nichtrami/led_tube/test_programs/results/analysis/tables/range_hidden_metrics_full.csv

Messpunkt | duration_s | packets_recv | packets_expected | packets_lost | loss_pct | loss_win_mean_pct | loss_win_p95_pct | loss_win_max_pct | burst_max_steps | burst_max_ms | win_visible_pct | win_clean_pct | jitter_mean_ms | rssi_mean_dbm | rssi_min_dbm | recv_per_seq_mean | recv_per_seq_min
10 m | 299.0 | 11934 | 11992 | 58 | 0.48 | 0.4452 | 0.0 | 30.91 | 3 | 75 | 1.6666666666666667 | 97.66666666666667 | 6.9603 | -81.22833333333334 | -95.0 | 4.802133333333333 | 2.34
50 m | 299.0 | 11743 | 11993 | 250 | 2.08 | 2.066 | 10.081500000000018 | 41.46 | 9 | 225 | 7.333333333333333 | 64.33333333333333 | 9.229566666666667 | -77.85066666666665 | -95.0 | 3.574666666666666 | 1.33
100 m | 299.0 | 10691 | 11993 | 1302 | 10.86 | 10.8079 | 36.635500000000015 | 87.8 | 23 | 575 | 37.0 | 25.666666666666664 | 16.4451 | -82.965 | -95.0 | 2.7185 | 1.2
150 m | 299.0 | 8732 | 11992 | 3260 | 27.18 | 27.146799999999995 | 60.79900000000006 | 82.93 | 28 | 700 | 80.0 | 0.6666666666666667 | 26.59283333333333 | -48.702333333333335 | -94.0 | 1.8716666666666666 | 1.17
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
