nichtrami/led_tube/test_programs/results/analysis/tables/range_hidden_summary.csv

Messpunkt | Verlust [%] | Fenster p95 [%] | Kopien je Seq. | Jitter [ms] | max. Ausfall [ms] | Fenster ab 50 ms [%] | RSSI [dBm]
10 m | 0.48 | 0.0 | 4.802133333333333 | 6.9603 | 75 | 1.6666666666666667 | -81.22833333333334
50 m | 2.08 | 10.081500000000018 | 3.574666666666666 | 9.229566666666667 | 225 | 7.333333333333333 | -77.85066666666665
100 m | 10.86 | 36.635500000000015 | 2.7185 | 16.4451 | 575 | 37.0 | -82.965
150 m | 27.18 | 60.79900000000006 | 1.8716666666666666 | 26.59283333333333 | 700 | 80.0 | -48.702333333333335
200 m | 36.29 | 63.67250000000001 | 1.6142666666666667 | 32.1195 | 950 | 95.66666666666667 | -77.394
