nichtrami/led_tube/test_programs/results/analysis/tables/range_metrics_full.csv

Messpunkt | duration_s | packets_recv | packets_expected | packets_lost | loss_pct | loss_win_mean_pct | loss_win_p95_pct | loss_win_max_pct | burst_max_steps | burst_max_ms | win_visible_pct | win_clean_pct | jitter_mean_ms | rssi_mean_dbm | rssi_min_dbm | recv_per_seq_mean | recv_per_seq_min
0 m | 299.0 | 11992 | 11992 | 0 | 0.0 | 0.0 | 0.0 | 0.0 | 0 | 0 | 0.0 | 100.0 | 4.144133333333334 | -81.644 | -93.0 | 4.999766666666667 | 4.88
10 m | 299.0 | 11992 | 11992 | 0 | 0.0 | 0.0 | 0.0 | 0.0 | 0 | 0 | 0.0 | 100.0 | 6.1621999999999995 | -82.39233333333334 | -96.0 | 4.988933333333333 | 4.55
50 m | 299.0 | 11985 | 11992 | 7 | 0.06 | 0.05813333333333333 | 0.0 | 2.5 | 1 | 25 | 0.0 | 97.66666666666667 | 5.817633333333333 | -81.50399999999999 | -96.0 | 4.622533333333332 | 4.15
100 m | 299.0 | 11981 | 11992 | 11 | 0.09 | 0.09090000000000001 | 0.0 | 7.14 | 3 | 75 | 0.33333333333333337 | 97.0 | 6.621566666666667 | -82.85266666666666 | -95.0 | 4.426966666666667 | 3.52
150 m | 299.0 | 11654 | 11991 | 337 | 2.81 | 2.7947 | 12.215000000000003 | 43.75 | 11 | 275 | 8.666666666666668 | 61.0 | 8.706700000000001 | -79.27233333333332 | -94.0 | 3.3871 | 1.87
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
