nichtrami/led_tube/test_programs/results/analysis/tables/range_summary.csv

Messpunkt | Verlust [%] | Fenster p95 [%] | Kopien je Seq. | Jitter [ms] | max. Ausfall [ms] | Fenster ab 50 ms [%] | RSSI [dBm]
0 m | 0.0 | 0.0 | 4.999766666666667 | 4.144133333333334 | 0 | 0.0 | -81.644
10 m | 0.0 | 0.0 | 4.988933333333333 | 6.1621999999999995 | 0 | 0.0 | -82.39233333333334
50 m | 0.06 | 0.0 | 4.622533333333332 | 5.817633333333333 | 25 | 0.0 | -81.50399999999999
100 m | 0.09 | 0.0 | 4.426966666666667 | 6.621566666666667 | 75 | 0.33333333333333337 | -82.85266666666666
150 m | 2.81 | 12.215000000000003 | 3.3871 | 8.706700000000001 | 275 | 8.666666666666668 | -79.27233333333332
200 m | 10.61 | 31.715500000000002 | 2.380933333333333 | 14.943833333333332 | 425 | 40.666666666666664 | -63.443000000000005
